Jonsmith9847/ROCO318/Renders/Bottom.jpg

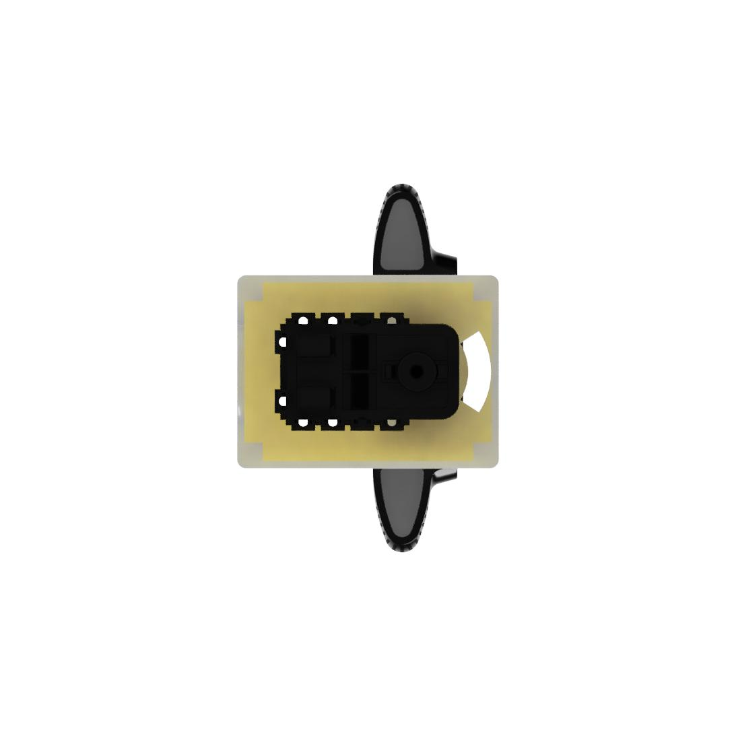
Renders/Bottom.jpg
