Jonsmith9847/ROCO318/Renders/Front.jpg

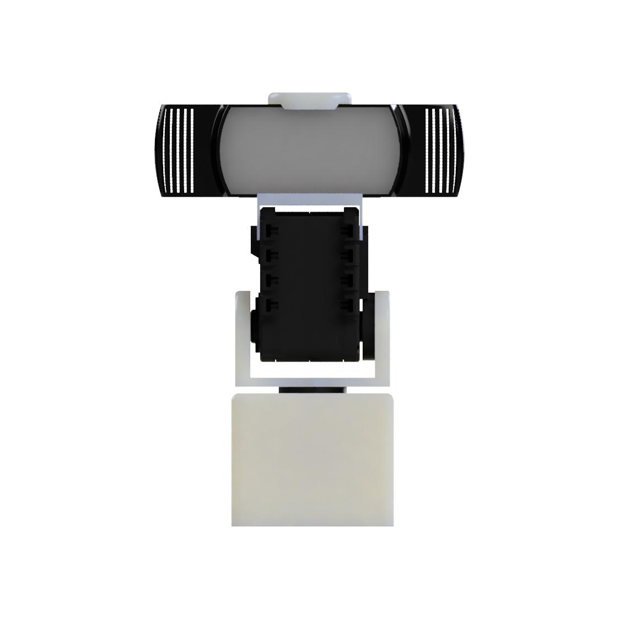
Renders/Front.jpg
