Jonsmith9847/ROCO318/Renders/IsometricFront.jpg

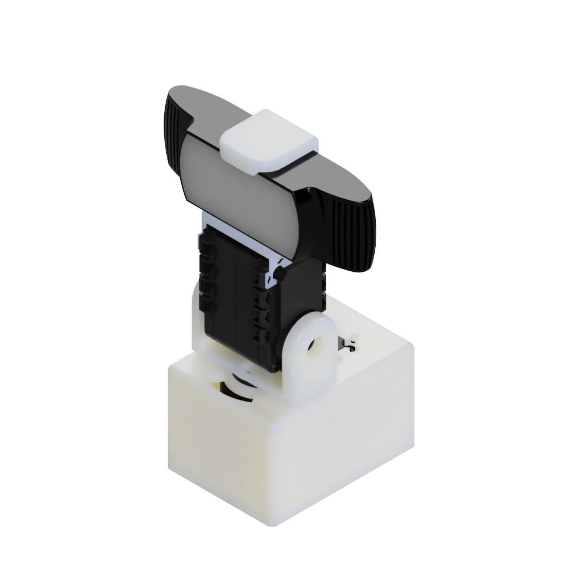
Renders/IsometricFront.jpg
